ShaunG-RU/DRC-Project/LTspice/RMS Based Compressor - Alternative Design/DRC.asc

Attack: res; 0
B2: bv; V=(white(2e6*time)/100)
C1: cap; 0.01µ
C2: cap; 0.01µ
C3: cap; 0.01µ
C4: cap; 22p
C5: cap; 10µ
C7: cap; 0.1µ
C10: cap; 1µ
C11: cap; 100p
D1: diode; 1N4148
D2: diode; 1N4148
D3: diode; 1N4148
D4: diode; 1N4148
R1: res; 20k
R2: res; 10k
R3: res; 20k; tol=1
R4: res; 10k
R5: res; 10k
R6: res; 52.3
R7: res; 4.7
R8: res; 2k
R9: res; 2k
R10: res; 162k
R11: res; 500
R12: res; 500
R13: res; 5.1k
R14: res; 2k
R15: res; 680k
R16: res; 10k
R17: res; 40k
R18: res; 2k
R19: res; 2k
R22: res; 243k
R23: res; 25k
R24: res; 25k
R29: res; 10Meg
R30: res; 10Meg
R31: res; 84.5k
R32: res; 750k
R33: res; 10Meg
THAT1: THAT2181A
U1: OP1177
U2: OP1177
U3: AD8310
U4: OP1177
U5: OP1177
U9: LTC1966
U12: LT1494
V1: voltage; 12
V2: voltage; -12
V3: voltage; 5
V4: voltage; -5
V5: voltage; wavefile=lickpick.wav
V6: voltage; 1.9
V7: voltage; wavefile=lickpick.wav
V8: voltage; 4
Named nets: INPUT, V+, V-, ABS, 0, Vdd, Vss, RMS, LOG, INPUT2, THRESHOLD, GAIN, VCA
.SUBCKT THAT2181A  1   2   3   4   5   6   7   8 
*(lin, Ec+, Ec-, Sym, Vee, GND, Vcc, Iout)
R1         10 13  2.5k  
R2         10 14  2.5k  
I1         10 29 DC 50uA  
R3         11 7  8k  
R4         12 7  8k  
G1         7 15 11 12 1.25e-4
R5         0 15  10MEG  
R6         0 16  10k  
C1         16 15  10p  
R7         19 7  2k  
G2         19 20 15 0 5e-4
C2         19 7  8p  
E1         20 28 30 0 2
R8         5 29  1.7k  
V1         0 29 DC 2.1V  
I2         0 30 DC 20uA  
R9         4 2  27  
C3         20 0  12p  
I3         20 28 DC 220uA  
V2         18 0 DC .7V  
V3         17 15 DC 1.4V  
Q1         11 1 13 QNHIB 
Q2         12 9 14 QNHIB 
Q3         20 21 23 QNPNNOM 
Q4         20 22 24 QNPNNOM 
Q5         8 4 27 QNPNNOM 
Q6         1 25 26 QNPNNOM 
Q7         1 2 23 QPNPNOM 
Q8         8 3 24 QPNPNOM 
Q9         28 28 27 QPNPNOM 
Q10        28 28 26 QPNPNOM 
Q11        28 29 5 QNPNNOM 
Q12        30 30 31 QNPNNOM 
Q13        0 0 31 QPNPNOM 
D1         18 15 DNOM 
D2         17 7 DNOM 
R10        3 25  22  
R11        22 20 22  
R12        21 20 27  
Vos        9 6 DC 3mV  
.model qnpnnom npn (is=1e-15 bf=200, vaf=110, cjc=3pF)
.model qpnpnom pnp (is=1e-15 bf=100, vaf=85, cjc=5pf)
.model qnhib npn (bf=16000)
.model dnom d (is=1e-15)
.ENDS
.tran 250m
