ShaunG-RU/DRC-Project/LTspice/Peak Detector/Peak Detector.asc

C1: cap; 10n
C2: cap; 4.7n
C3: cap; 10n
C4: cap; 4.7n
C5: cap; 100n
D1: diode; 1N4148
D2: diode; 1N4148
D3: diode; 1N4148
D4: schottky; CMDSH2-3
D5: schottky; CMDSH2-3
D6: schottky; BAT54
D7: diode; 1N4148
D8: diode; 1N4148
D9: schottky; BAT54
Q1: npn
Q2: npn
R1: res; 47k
R2: res; 47k
R3: res; 100
R4: res; 10k
R5: res; 33
R6: res; 10Meg
R7: res; 10k
R8: res; 10k
R9: res; 10k
R10: res; 1k
R11: res; 10k
R12: res; 10k
R13: res; 33
R14: res; 10Meg
R15: res; 10k
R16: res; 100k
R17: res; 10k
R18: res; 10k
R19: res; 1k
R20: res; 10k
R21: res; 10k
R22: res; 200
R23: res; 200
R24: res; 500k
U1: AD549
U2: AD549
U3: AD549
U4: AD549
U5: AD549
U6: AD549
U7: AD549
U8: AD549
V1: voltage; PULSE(0 1 0 1p 1p 100u 200u 5)
V2: voltage; -15
V3: voltage; 15
V4: voltage; SINE(0 1 10000 2.5m 0 0 5)
V5: voltage; SINE(0 3 10000 5m)
Named nets: 0, ABS, PEAK2, Vss, PEAK, PEAK3, V+, V-, PEAK0, Vdd
.tran 5m
