ShaunG-RU/DRC-Project/LTspice/Envelope Detector with Attack and Release Control/envelope det.asc

C1: cap; 1µ
C2: cap; 10µ
C3: cap; 10µ
D1: diode
D2: diode
D3: diode
D4: diode
R1: res; 20k
R2: res; 20k
R3: res; 100k
R4: res; 1k
R5: res; 10k
U1: AD549
U2: AD549
U3: AD549
U4: AD549
V1: voltage; SINE(0 1 1k)
V2: voltage; 15
V3: voltage; -15
Named nets: V+, V-, 0
.tran 10m
