ShaunG-RU/DRC-Project/LTspice/RMS and Peak Based Compressor with Knee Control/Knee Control DRC.asc

B1: bv; V=1.414*0.775*(10**({dBu_level}/20))*V(1V)
B2: bv; V=V(1V)*sin({modfreq}*2*pi*time)
B3: bv; V=20*log10(abs(V(signal_in))) -20*log10(abs(V(final)))
B4: bv; V=V(final)/(1.414*0.775*(10**({dBu_level}/20)))
C1: cap; 0.1µ; V=50 Irms=0 Rser=0.09 Lser=0
C2: cap; 0.1µ
C3: cap; 0.2n; V=25 Rser=0.2
C4: cap; 0.3n; V=50 Irms=0 Rser=0.1 Lser=0
C5: cap; 0.1µ; V=10 Irms=0 Rser=0.003 Lser=0
C6: cap; 10µ; Rser=0.09
C8: cap; 22p; V=50 Irms=0 Rser=0.1601 Lser=520p mfg="Würth Elektronik" pn="885012008039 WCAP-CSGP 1206" type="NP0"
C9: cap; 1µ
C10: cap; 0.1µ; V=10 Irms=0 Rser=0.003 Lser=0
C11: cap; 0.3n; V=50 Irms=0 Rser=0.1 Lser=0
C12: cap; 1µ
C13: cap; 0.1µ; V=10 Irms=0 Rser=0.003 Lser=0
C14: cap; 0.2n; V=25 Rser=0.2
C15: cap; 1µ
C16: cap; 10µ
C17: cap; 1µ
C18: cap; 0.1µ; V=50 Irms=0 Rser=0.09 Lser=0
C19: cap; 0.1µ
D1: diode; 1N4148
D2: diode; 1N4148
D3: diode; 1N4148
D4: diode; 1N4148
D5: diode; 1N4148
D8: diode; 1N4148
D10: schottky; RB500SM-30
D12: diode; 1N4148
D14: diode; 1N4148
D19: diode; 1N4148
I1: current; 255.8µ
Q1: npn; 2N3904
Q2: npn; 2N3904
R1: res; 47.6K
R2: res; 10K
R3: res; 6.8K
R4: res; 6.8K
R5: res; 6.8K
R6: res; 3.4K
R7: res; 6.8K
R8: res; 4.2k
R9: res; 4.2k
R10: res; 5k
R11: res; 2K
R12: res; 2K
R13: res; 100K
R14: res; 100K
R15: res; 100K
R16: res; 100K
R17: res; 10K
R18: res; 10K
R19: res; 10K
R20: res; 10K
R21: res; 1k
R22: res; 10k
R23: res; 10k
R24: res; 10K
R25: res; 10K
R26: res; 35k
R27: res; {release}
R28: res; {attack}
R29: res; {attack}
R30: res; 10k
R31: res; 10k
R32: res; 10K
R33: res; 10K
R34: res; 250
R36: res; 10k
R37: res; 10K
R40: res; 10k
R41: res; 1k
R42: res; 1k
R43: res; 20
R44: res; 10K
R45: res; 10K
R46: res; 1k
R47: res; 4k
R48: res; 1k
R49: res; 1k
R50: res; 10k
R51: res; 10k
R52: res; 100k
R53: res; 100k
R54: res; 100k
R55: res; 100k
R56: res; 10k
R57: res; 10k
R58: res; 20K
R59: res; 20K
R60: res; 10Meg
R61: res; 5.1K
R62: res; 14k
R63: res; 100k
R65: res; {tanh_gain_in}
R66: res; 10k
R67: res; 250
R68: res; 10k
R69: res; 10k
R71: res; 1k
R72: res; 2k
R73: res; 10k
R74: res; 30.808k
R75: res; 1k
R76: res; 30.808k
R77: res; 1k
R78: res; 1k
R80: res; 200k
R81: res; 100k
R82: res; 20
R83: res; 1k
R84: res; 4k
R85: res; 100k
R86: res; 100k
R87: res; 10k
R88: res; 10k
R89: res; 10k
U1: TL072
U2: LTC6244
U3: LTC6244
U4: TL072
U5: TL072
U6: TL072
U7: TL072
U8: pot; T={threshold}
U9: TL072
U10: TL072
U11: pot; R=1k; T= 1/{ratio_ctrl} stiff=10000
U12: TL072
U13: TL072
U14: LT1217
U15: TL072
U16: TL072
U17: pot; T={knee}
U18: TL072
U19: TL072
U20: TL072
U21: TL072
U22: TL072
U23: VCA824
U24: TL072
U25: TL072
U26: pot; T=.4917
U27: TL072
U28: THAT2180A
U29: TL072
U30: TL072
U31: TL072
U32: LTC6244
U33: LT1217
U35: TL072
U36: LTC6244
U37: LT1217
U38: TL072
U39: pot; R=1meg; T=.8029
U40: LTC6244
U41: VCA824
U42: pot; T=.4917
U43: pot; R=1meg; T=.8033
U44: TL072
U45: LTC6244
U46: TL072
U47: TL072
V2: voltage; +15V
V3: voltage; -15V
V4: voltage; SINE(0 1 {freq})
V5: voltage; PULSE(-1 1 0 {1/(2*freq)} {1/(2*freq)} 0 {1/freq})
V6: voltage; 5V
V7: voltage; ""; AC 1.736
V8: voltage; 5V
V9: voltage; 0V
V10: voltage; PULSE(-1 1 0 1e-6 1e-6 {duty/freq} {1/freq})
V11: voltage; PULSE(0 1 20ms 1e-6 1e-6 0.1 0 1)
V12: voltage; -5V
V17: voltage; 0
V19: voltage; SINE(0 0.1 50)
V20: voltage; -0.5V
X1: 
X3: 
X4: 
X5: 
X6: 
X7: 
X8: 
X9: 
X10: 
X11: 
X12: 
X13: 
X14: 
X15: 
X16: 
X17: 
X18: 
X19: 
X20: 
X21: 
X22: 
X23: 
Named nets: 0, +15V, -15V, 1V, full_rect, full_rect_log, 1Vramp, tanh_out, full_rect_log_min_thr, thr_log, peak_AR, gain_before_ratio, gain_before_ratio_inv, 1Vmod, gain_after_ratio, +5V, -5V, signal_in, final, gain_final, tanh_out_gain_inv, tanh_out_clamp, vratio_buf, tanh_out_clamp2, tanh_out_clamp2_clip_buf, peak_AR_buf_tanh, gain_reduction, final_norm, lin_thr, vratio, vratio_buf_inv, 1Vsquare, signal_in_ac, tanh_norm, vratio_buf_sym, -0.5V, tanh_out_shift, full_rect_log_min_thr_clip2, 1Vpulse, full_rect_log_min_thr_clip, vhalf_kw, vhalf_kw_inv, full_rect_log_min_thr_min_half_kw, 4dBu, vhalf_kw_buf
Conversion from 1V max to dBu_level.
Circuit nominal is 4dBu
1V reference sine for tests
PRECISION FULL WAVE RECTIFIER
linear to log signal converter
gain 5.76 so that we get 10V at 4dBU for rectifier stage
op amp buffer to make output impedance as low as possible 
as the following rectifier stage is sensitive to it
log stage transfer function Vout=   -Vt*ln(Vin/(Is*R))
Vt = diode thermal voltage, Is = diode saturation current
thermal voltage depends on absolute temperature, which would go up with room temperature
and high signal levels (more current flowing in the diodes = more heat)
thermal management may be advised, ex: both diodes for signal and threshold could be termally
coupled.
Also advised to match both diodes
linear to log threshold converter
THRESHOLD POT
out = full_rect_log - thr_log
thr_log more negative = higher threshold
wiper closer to 1 = lower threshold
wiper closer to 0 = higher threshold
LOG DOMAIN PEAK DETECTOR +  EXP A/R
release potentiometer
attack potentiometer
input offset compensation
output offset compensation
RAILS
.param modfreq = {10}
.param freq = {20}
What we have is a smooth transition between unity gain setpoint (0V), ratio = 1
and set ratio voltage.
1V amplitude modulated sine for tests
1V triangle
gain reduction quick&dirty (zoom to get rid of singularities)
.tran 0 0.2 1ms {1/sample_rate} uic
.param dBu_level = {4}
.param sample_rate = 44.1k
.options cshunt=1e-15
TEST BENCH
compressor output
KNEE MANAGEMENT
SIGNAL(dB) - THRESHOLD(dB) STAGE
tanh() cell using a BJT differential pair
tanh() saturation... low R65 looks more like sine. (very soft knee)
 very high R65 introduces high distortion at knee. (folding)
RATIO POT
clamp tanh_out_gain_inv output positive excursions to -vratio level (positive value).
should not happen unless tanh() current sink is above 247µA.
then,  tanh_out_gain_inv may go above -vratio.
gain = gain_before_ratio*( 1 - 1/ratio)
gain = gain_before_ratio + gain_before_ratio_inv/ratio  (gain_after_ratio_inv is negative)
gain = gain_before_ratio + gain_after_ratio (gain_after_ratio is negative)
AUDIO PATH VCA STAGE - FEEDFORWARD
;ac dec 10 20 100000
1V square
.param duty = {0.5}
Here 0V level is threshold +kw/2. The point at which the compressor should start working
we clip signal under 0V
lin_v = 15*(1-t)*10k/(10k +5k)
the incentive to use a lin to log diode converter instead of a log pot is :
use the same transfer function. (make calibration easier)
have the thermal effect partially cancel each other (since both diode networks heat more or less
the same way, but that is assuming current is the same which is not because the threshold
diode  is subject to DC)
The peak detector A/R stage contribution is made negligible by setting the fastest A/R possible,
R=100 ohms for both
we ommit input gain = 5.76 because both vin and vthr use the same gain so it cancels out.
technically we could ommit Is*R because they also cancel out...
 
n*-Vt*ln(Vin/(Is*R))
25.4mV*ln(Vin/(2nA*4.2k))
deltaVln = 25.4mV*ln(Vin/(2nA*4.2k)) - 25.4mV*ln(Vthr/(2nA*4.2k)) 
deltaVln = 25.4mV*(ln(Vin/(2nA*4.2k)) - ln(Vthr/(2nA*4.2k)))
deltaVln = 25.4mV*(ln(Vin) - ln(Vthr)  -ln(2nA*4.2k) + ln(2nA*4.2k))
 
now convert ln2 to log10, hence the factor 2.303 and then to dBV...
 
deltaVllog = (25.4mV*2.303)*(log(Vin) - log(Vthr))
deltaVllog = (25.4mV*2.303)*(log(Vin) - log(Vthr))
dbV = 20*log(V)
we want k*25.4mV*2.303 = 20
k =20/(2.303-*25.4mV)
k = 341.9
and we also have THAT2180 1 dbV gain = 0.0061V
thus final normalization gain = 341.9*0.0061 = 2.08559
k = 2.08559
use good audio cap here
gain_final OUTPUT impedance should be as low as possible to drive THAT2180 properly
Z_out << 50 Ohms.
compare that to TL072 125ohms open loop resistance.
That's why we use a high current low output impedance LT1217 Op Amp
gain_in 1 + R74/R75 (here 30.808/1 +1 = 31.808) so that we renormalize to 10V max
max log_min_thr (4dbU triangle signal, threshold -INF dB) =  0.31425V
we're back to 0.314V max
R67 current limiting resistor to protect U14
R79 current limiting resistor to protect U33
THEORY = 25.4mV*ln(Vin*5.76/(2nA*4.2k))
 25.4mV*ln(10/(2nA*4.2k)) = 0.355325
gain_before ratio has to stay under 1.6V !!! as per VCA824 datasheet
;.noise V(final) V7 dec 10 1 20000
0.1% or less
0.1% or less
0.1% or less
0.1% or less
D8 and D4 must be matched and coupled thermally
input offset compensation
output offset compensation
input signal amplitude could be as high as 10V
symmetry point is 0.5V this is an inverting op amp with 0.5V reference symmetry.
used to properly condition the gain signal of the VCA824 (U41) that performs tanh() normalization
inverting op amp
tanh() normalizer ( so that : vratio_buf < tanh_norm < 0V )
this assumes that the previous tanh() cell is well behaved and  -0.5V < tanh_out < 0.5V
if not, the following clamping stage will take care of unwanted excursions.
a bit of extra precaution so that VG fed to the U23 VCA824 never goes above 0V.
tanh() normalization and clamping action is not perfect, as well as U41 VCA824 always 
has some offset despite calibration, so we clip above 0V here.
clamping is also required if tanh() current source is also set above 247µA
tweak 200 < R65 < 1.5k
.param bw = {0.05}
here we clip signal under -kw/2 and above kw/2 0V is threshold
bw is the threshold bandwidth for soft/hard knee application
setting I1 above 247µA gives a tanh() output that is no more bound from [-0.5V to 0.5V]
Normalization and shifting to 0.5 is no more sufficient to set final ratio signal inside [vratio, 0V] range. 
however, clamping at -vratio and clipping at 0V before the U23 VCA824 make the
circuit compensated once again should that happen.
1V square pulse
for testing A/R constants
account for diode drop in final gain.
attack range 100 - 10k
release range 10k - 10Meg
RATIO = 1/T
vratio =  T - 1
GAIN COMPUTER (U23 with variable ratio for knee management and U25 for final gain)
FINAL GAIN NORMALIZATION
CURRENT TO VOLTAGE
CURRENT LIMITING
KNEE WIDTH POT
KW = 1 - T
We offset down the selected threshold by half knee width.
This to ensure smooth knee application, so that the gain computer and knee width start
working at the same levels
decoupling A/R with diodes is one way to do it, but it introduces a diode voltage drop.
It is mainly experimental. The more standard way is to use separate attack/release stages
separated by a buffer
the sidechain and the audio path branches before the capacitor and each uses different caps
it may create phase problems. You can try using a single cap.
quite experimental. may introduce distortion for small knee widths (hard knee = distortion)
this is because of the use of the tanh() function
.param knee=0.95
.param ratio_ctrl=100
.param threshold = 0.5
LP filter potentiometer
.param attack = 100
.param release = 100
COMPRESSOR PARAMETERS
;.step param knee 0.85 0.98 0.02
;.step param ratio_ctrl 1 50 5
;.step param attack 0.3 1 0.1
.step dec param tanh_gain_in 100 10000 3
.param tanh_gain_in = 4000
35.3456k
ratio_ctrl not the actual ratio
APPROXIMATIVE TABLE :
ratio_ctrl      ratio
6                 1.31
11                1.85
16                2.47
21                3.22
26                4.11
31                5.22
36                6.25
41                8.4
46                10.2
51                 12.2
;.step param threshold 0.1 1 0.1
www.skynext.tech
Author : R.Verissimo
release 0.91 05/09/2023
.SUBCKT pot 1 2 3 T=0.5 R=10k
.param tap={limit(T,1m,.999)}
R0 1 3 {R*(1-tap)}
R1 3 2 {R*tap}
.ENDS
 
.SUBCKT exppot 1 2 3 T=0.5
.param tap={limit(T,1m,.999)}
.param stiff={limit(stiff,1,10000)}
 
R0 1 3 {R*exp(-tap*ln(R*stiff))}
R1 3 2 {R*(1-exp(-tap*ln(R*stiff)))}
.ENDS
*                 Iin          
*                  |  Ec+ 
*                  |   |   Ec-
*                  |   |   |  Vee 
*                  |   |   |   |  GND
*                  |   |   |   |   |  Vcc 
*                  |   |   |   |   |   |  Iout
*                  |   |   |   |   |   |   |
.SUBCKT THAT2180A  1   2   3   4   5   6   7 
*
*
*
R1         10 13  2.5k  
R2         10 14  2.5k  
I1         10 29 DC 50uA  
R3         11 7  8k  
R4         12 7  8k  
G1         7 15 11 12 1.25e-4
R5         0 15  10MEG  
R6         0 16  10k  
C1         16 15  10p  
R7         19 7  2k  
G2         19 20 15 0 5e-4
C2         19 7  8p  
E1         20 28 30 6 2
R8         5 29  1.7k  
V1         0 29 DC 2.1V  
I2         0 30 DC 20uA  
R9         4 2  27  
C3         20 0  12p  
I3         20 28 DC 220uA  
V2         18 0 DC .7V  
V3         17 15 DC 1.4V  
Q1         11 1 13 QNHIB 
Q2         12 9 14 QNHIB 
Q3         20 21 23 QNPNNOM 
Q4         20 22 24 QNPNNOM 
Q5         8 4 27 QNPNNOM 
Q6         1 25 26 QNPNNOM 
Q7         1 2 23 QPNPNOM 
Q8         8 3 24 QPNPNOM 
Q9         28 28 27 QPNPNOM 
Q10        28 28 26 QPNPNOM 
Q11        28 29 5 QNPNNOM 
Q12        30 30 31 QNPNNOM 
Q13        0 0 31 QPNPNOM 
D1         18 15 DNOM 
D2         17 7 DNOM 
R10        3 25  20  
R11        22 20 20 
R12        21 20 27  
Vos        9 6 DC 3mV  
Isym       0 4 DC -420nA  
*    Isym = -420nA for typical THD.  Set to -1uA for worst case THD.
.model qnpnnom npn (is=1e-15 bf=200, vaf=110, cjc=3pF)
.model qpnpnom pnp (is=1e-15 bf=100, vaf=85, cjc=5pf)
.model qnhib npn (bf=16000)
.model dnom d (is=1e-15)
.ENDS
*                      Positive Supply
*                      |   Gain Control
*                      |   |   Non-Inverting Input 
*                      |   |   |   Gain Setting Resistor Terminals
*                      |   |   |     |   |  Inverting Input
*                      |   |   |     |   |    |  Negative Supply
*                      |   |   |     |   |    |   |  Reference Voltage 
*                      |   |   |     |   |    |   |   |  Output
*                      |   |   |     |   |    |   |   |    |
*                      |   |   |     |   |    |   |   |    |    Feedback
*                      |   |   |     |   |    |   |   |    |      |
.SUBCKT VCA824 +Vcc VG +Vin +Rg -Rg -Vin -Vcc Vref Out Gnd FB
 
X_U5_F8    U5_N00257 U5_N00297 N09821 -VCC VCA82X_BIAS_U5_F8 
X_U5_F1    U5_N00167 U5_N00177 +VCC N06304 VCA82X_BIAS_U5_F1 
V_U5_V1         U5_N00167 U5_N00195 0.433V
E_U5_E1         U5_N00195 -VCC +VCC -VCC 0.5
X_U5_F6    U5_N00297 U5_N00251 N08923 -VCC VCA82X_BIAS_U5_F6 
X_U5_F3    U5_N00177 U5_N00183 +VCC N08572 VCA82X_BIAS_U5_F3 
X_U5_F4    U5_N00183 U5_N00189 +VCC N08740 VCA82X_BIAS_U5_F4 
X_U5_F2    U5_N00189 U5_N00257 +VCC N10100 VCA82X_BIAS_U5_F2 
X_U5_F5    U5_N00251 U5_N00205 N07015 -VCC VCA82X_BIAS_U5_F5 
R_U5_R3         U5_N00195 U5_N00205  1k  
Q_U6_Q24         N06304 U6_N16946 U6_N15431 NPN8 {x1}
R_U6_R15         U6_N26012 +VCC  300  
R_U6_R20         U6_N49467 U6_N46592  100  
R_U6_R24         -VIN U6_N336522  150  
Q_U6_Q23         U6_N00503 U6_N16946 U6_N13215 NPN8 {x6}
C_U6_C3         U6_N334753 U6_N334801  10m  TC=0,0 
C_U6_C1         U6_N00709 U6_N22036  0.5p  
Q_U6_Q28         U6_N22036 U6_N07222 U6_N26012 PNP8 {x6}
Q_U6_Q29         U6_N07222 U6_N07222 U6_N612661 PNP8 {x2}
Q_U6_Q37         U6_N49467 U6_N16946 U6_N49758 NPN8 {x6}
R_U6_R13         -VCC U6_N19410  2k  
D_U6_U1         U6_N334753 U6_N334759 dn3 
R_U6_R21         U6_N57293 +VCC  300  
Q_U6_Q30         N07015 U6_N07222 U6_N29549 PNP8 {x2}
R_U6_R18         -VCC U6_N36767  160  
R_U6_R25         U6_N3853581 +RG  10  
Q_U6_Q32         +RG U6_N16946 U6_N36767 NPN8 {x6}
E_U6_E1         U6_N00709 -VCC +VCC -VCC 0.5
R_U6_R23         +VIN U6_N336330  150  
Q_U6_Q36         U6_N46276 U6_N46276 U6_N46592 NPN8 {x14}
I_U6_I1         U6_N334759 U6_N334753 DC 1.5u  
Q_U6_Q26         U6_N16946 U6_N16946 U6_N19410 NPN8 {x2}
Q_U6_Q25         +VCC N06304 U6_N16946 NPN8 {x2}
Q_U6_Q40         U6_N42606 U6_N07222 U6_N57293 PNP8 {x6}
Q_U6_Q22         U6_N04782 U6_N04782 U6_N10900 NPN8 {x14}
Q_U6_Q21         +VCC U6_N336330 U6_N04782 NPN8 {x14}
R_U6_R14         U6_N612661 +VCC  2k  
R_U6_R17         -VCC U6_N13215  160  
Q_U6_Q34         +VCC U6_N336522 U6_N46276 NPN8 {x14}
Q_U6_Q33         N08372 U6_N22036 +RG NPN8 {x14}
R_U6_R22         -VCC U6_N51427  160  
E_U6_E2         U6_N334759 -VCC +VCC -VCC 0.5
R_U6_R19         -VCC U6_N49758  160  
Q_U6_Q27         U6_N22036 +RG U6_N00503 NPN8 {x14}
Q_U6_Q31         -VCC N07015 U6_N07222 PNP8 {x2}
C_U6_C2         U6_N00709 U6_N42606  0.5p  
Q_U6_Q38         U6_N42606 -RG U6_N49467 NPN8 {x14}
X_U6_F1    U6_N334801 U6_N334759 U6_N336330 U6_N334759
+  VCA82X_INPUT_BUFFER_U6_F1 
R_U6_R11         U6_N29549 +VCC  900  
E_U6_E4         U6_N3853202 -VCC +VCC -VCC 0.5
Q_U6_Q39         -RG U6_N16946 U6_N51427 NPN8 {x6}
R_U6_R16         U6_N00503 U6_N10900  100  
R_U6_R12         -VCC U6_N15431  955  
Q_U6_Q35         N08468 U6_N42606 -RG NPN8 {x14}
C_U6_C5         U6_N3853202 U6_N3853581  0.88p  TC=0,0 
R_U7_R27         -VCC U7_N01059  800  
Q_U7_Q56         U7_N65219 U7_N65219 U7_N64914 NPN8 {x4}
Q_U7_Q60         U7_N107420 U7_N89137 U7_N81704 NPN8 {x12}
Q_U7_Q86         U7_N168308 U7_N167450 U7_N168596 NPN8 {x16}
Q_U7_Q77         U7_N137141 U7_N137141 U7_N142127 PNP8 {x16}
R_U7_R25         GND U7_N89137  50  
R_U7_R23         -VCC U7_N01019  100  
Q_U7_Q59         U7_N86791 U7_N65219 U7_N01059 NPN8 {x1}
R_U7_R28         -VCC U7_N01061  200  
R_U7_R32         GND U7_N160714  50  
R_U7_R17         -VCC U7_N55967  100  
R_U7_R37         U7_N145504 +VCC  110  
Q_U7_Q45         U7_N34597 U7_N34597 U7_N34298 PNP8 {x12}
Q_U7_Q87         U7_N167450 U7_N167450 U7_N168824 NPN8 {x16}
Q_U7_Q84         U7_N165781 U7_N165781 U7_N168308 NPN8 {x16}
Q_U7_Q62         U7_N01231 U7_N65219 U7_N01061 NPN8 {x4}
R_U7_R11         U7_N34298 +VCC  160  
Q_U7_Q79         U7_N01317 U7_N142759 U7_N145504 PNP8 {x16}
Q_U7_Q80         N08740 U7_N01231 U7_N137141 PNP8 {x16}
Q_U7_Q52         U7_N53649 U7_N65219 U7_N55659 NPN8 {x8}
R_U7_R22         U7_N81704 U7_N82314  1k  
Q_U7_Q49         U7_N01387 U7_N01387 U7_N37408 PNP8 {x12}
R_U7_R21         U7_N01001 +VCC  740  
Q_U7_Q78         U7_N142759 U7_N142759 U7_N145276 PNP8 {x16}
R_U7_R13         U7_N1695201 VG  50  
Q_U7_Q61         U7_N116536 U7_N86791 U7_N82314 NPN8 {x12}
Q_U7_Q88         N08740 U7_N160714 N08923 NPN8 {x2}
Q_U7_Q65         U7_N01387 U7_N01387 U7_N107420 NPN8 {x12}
Q_U7_Q63         U7_N01317 U7_N65219 U7_N01207 NPN8 {x4}
R_U7_R34         U7_N142127 +VCC  110  
Q_U7_Q85         FB U7_N165781 U7_N167450 NPN8 {x16}
R_U7_R39         N08923 U7_N1690600  50  
Q_U7_Q70         U7_N119904 U7_N119904 U7_N122147 PNP8 {x16}
R_U7_R29         -VCC U7_N01207  200  
Q_U7_Q55         N08572 U7_N65219 U7_N67656 NPN8 {x2}
Q_U7_Q71         U7_N122683 U7_N122683 U7_N119904 PNP8 {x16}
R_U7_R31         -VCC U7_N168596  200  
Q_U7_Q68         U7_N116528 U7_N116512 U7_N01001 PNP8 {x12}
Q_U7_Q69         U7_N116536 U7_N116536 U7_N116528 PNP8 {x12}
Q_U7_Q74         U7_N122683 U7_N01351 N08468 NPN8 {x16}
R_U7_R26         U7_N86791 GND  4.1k  
R_U7_R24         -VCC U7_N01017  100  
Q_U7_Q57         U7_N81704 U7_N65219 U7_N01017 NPN8 {x8}
R_U7_R38         U7_N122147 +VCC  110  
Q_U7_Q47         U7_N37110 U7_N34597 U7_N34058 PNP8 {x12}
Q_U7_Q51         U7_N01387 U7_N45862 U7_N53649 NPN8 {x12}
Q_U7_Q46         U7_N01351 U7_N37408 U7_N34597 PNP8 {x12}
Q_U7_Q50         U7_N01351 U7_N1695201 U7_N51592 NPN8 {x12}
R_U7_R18         -VCC U7_N55659  100  
Q_U7_Q81         FB U7_N01317 U7_N142759 PNP8 {x16}
R_U7_R16         -VCC U7_N67656  400  
R_U7_R15         U7_N51592 U7_N53649  1k  
Q_U7_Q66         U7_N116512 U7_N116512 U7_N01003 PNP8 {x12}
R_U7_R35         U7_N145276 +VCC  110  
Q_U7_Q72         U7_N122683 U7_N01351 N08372 NPN8 {x16}
R_U7_R19         -VCC U7_N64914  1.4k  
Q_U7_Q58         U7_N82314 U7_N65219 U7_N01019 NPN8 {x8}
R_U7_R30         -VCC U7_N168824  200  
R_U7_R20         U7_N01003 +VCC  740  
R_U7_R12         U7_N34058 +VCC  160  
Q_U7_Q53         U7_N51592 U7_N65219 U7_N55967 NPN8 {x8}
Q_U7_Q76         U7_N01231 U7_N137141 U7_N141896 PNP8 {x16}
Q_U7_Q54         +VCC N08572 U7_N65219 NPN8 {x4}
Q_U7_Q67         U7_N107420 U7_N116536 U7_N116512 PNP8 {x12}
R_U7_R36         U7_N141896 +VCC  110  
R_U7_R33         U7_N142127 U7_N145276  2k  
Q_U7_Q73         U7_N01231 U7_N01387 N08372 NPN8 {x16}
Q_U7_Q75         U7_N01317 U7_N01387 N08468 NPN8 {x16}
Q_U7_Q48         U7_N37408 U7_N37408 U7_N37110 PNP8 {x12}
Q_U7_Q64         U7_N01351 U7_N01351 U7_N107420 NPN8 {x12}
R_U7_R14         GND U7_N45862  50  
Q_U7_Q82         U7_N165781 U7_N1690600 N08740 PNP8 {x16}
Q_U8_Q38         U8_N01099 U8_N38844 U8_N39084 PNP8 {x14}
R_U8_R18         U8_N01099 U8_N82756  125  
Q_U8_Q49         U8_N78893 U8_N78893 U8_N80276 NPN8 {x5}
E_U8_E2         U8_N389559 -VCC +VCC -VCC 0.5
R_U8_R24         U8_N163888 FB  0.01  
R_U8_R23         VREF U8_N52536  10  
R_U8_R10         U8_N23775 U8_N13605  600  
Q_U8_Q47         U8_N75689 U8_N78893 U8_N73458 NPN8 {x3}
R_U8_R13         U8_N00843 U8_N13605  250  
X_U8_F1    U8_N389453 U8_N389559 VREF U8_N389559 VCA821_4_OUTPUT_STAGE_U8_F1 
Q_U8_Q45         U8_N63102 N10100 U8_N66552 NPN8 {x2}
C_U8_C7         U8_N00839 U8_N13605  0.85p  TC=0,0 
Q_U8_Q39         U8_N13605 U8_N38844 U8_N84507 NPN8 {x14}
Q_U8_Q52         OUT U8_N91269 -VCC NPN8 {x60}
Q_U8_Q36         U8_N39084 U8_N31052 U8_N32378 PNP8 {x6}
R_U8_R16         U8_N01099 U8_N80276  150  
Q_U8_Q43         U8_N75689 U8_N63102 U8_N163888 PNP8 {x8}
R_U8_R21         +VCC U8_N13605  20  
Q_U8_Q50         U8_N84507 U8_N78893 U8_N82756 NPN8 {x6}
C_U8_C8         U8_N01099 U8_N80276  0.85p  TC=0,0 
Q_U8_Q33         U8_N01025 N09821 U8_N24027 PNP8 {x2}
Q_U8_Q41         U8_N35588 U8_N01025 U8_N163888 NPN8 {x8}
R_U8_R11         U8_N01099 U8_N67452  600  
D_U8_D14         U8_N73458 U8_N01099 DX 
Q_U8_Q42         U8_N63102 U8_N63102 U8_N52536 PNP8 {x8}
Q_U8_Q35         U8_N31052 U8_N31052 U8_N00839 PNP8 {x5}
Q_U8_Q32         U8_N24027 U8_N24027 U8_N23775 PNP8 {x2}
Q_U8_Q51         U8_N91269 U8_N91269 -VCC NPN8 {x60}
D_U8_D17         U8_N163888 U8_N1399050 DX 
Q_U8_Q62         U8_N01099 U8_N38844 U8_N39084 PNP8 {x8}
Q_U8_Q61         U8_N13605 U8_N38844 U8_N84507 NPN8 {x8}
D_U8_U1         U8_N389449 U8_N389559 dn3
Q_U8_Q34         U8_N35588 U8_N31052 U8_N00843 PNP8 {x3}
C_U8_C2         U8_N38844 U8_N13605  0.89p  
D_U8_D18         U8_N1399050 U8_N52536 DX 
R_U8_R12         U8_N01099 U8_N67680  600  
Q_U8_Q59         U8_N114858 U8_N114858 +VCC PNP8 {x60}
D_U8_D16         U8_N1375710 U8_N163888 DX 
Q_U8_Q46         U8_N66552 U8_N66552 U8_N67680 NPN8 {x2}
Q_U8_Q44         N10100 U8_N66552 U8_N67452 NPN8 {x2}
Q_U8_Q60         OUT U8_N114858 +VCC PNP8 {x60}
R_U8_R14         U8_N00839 U8_N13605  150  
Q_U8_Q58         U8_N114858 U8_N39084 OUT NPN8 {x60}
I_U8_I1         U8_N389559 U8_N389449 DC 3.12u  
Q_U8_Q37         U8_N38844 U8_N35588 U8_N31052 PNP8 {x3}
R_U8_R17         U8_N32378 U8_N13605  125  
C_U8_C3         U8_N01099 U8_N38844  0.89p  
R_U8_R9         U8_N19796 U8_N13605  600  
Q_U8_Q48         U8_N38844 U8_N75689 U8_N78893 NPN8 {x3}
R_U8_R19         -VCC U8_N01099  20  
D_U8_D12         U8_N13605 U8_N00839 DX 
Q_U8_Q31         N09821 U8_N24027 U8_N19796 PNP8 {x2}
D_U8_D13         U8_N52536 U8_N1375710 DX 
R_U8_R25         OUT OUT  10  
Q_U8_Q53         U8_N91269 U8_N84507 OUT PNP8 {x60}
C_U8_C6         U8_N389449 U8_N389453  10m  
D_U8_D11         U8_N13605 U8_N00843 DX 
Q_U8_Q40         U8_N01025 U8_N01025 U8_N52536 NPN8 {x8}
R_U8_R15         U8_N01099 U8_N73458  250  
D_U8_D15         U8_N80276 U8_N01099 DX 
 
.PARAM  x4={x2*2} x5={x1*5} x12={x6*2} x6={x2*3} x24={x1*24} x8=1 x14={x2*7}
+  x16={x8*2} x18={x1*18} x90={x1*90} x60={x12*5} x1={x2/2} x2={x8/4} x30={x1*30}
+  x3={x1*3}
 
.MODEL DN3 D( IS=.1F AF=1.0 KF=39.0E-17)
 
.model dx       d(is=0.1p rs=.1 cjo=2p tt=1p bv=100 ibv=0.1p)
 
.model NPN8 npn
 
+ is=7.604e-018
+ bf=157
+ nf=1
+ vaf=78.71
+ ikf=0.03975
+ ise=3.219e-014
+ ne=2
+ br=0.7614
+ nr=1
+ var=1.452
+ ikr=0.08172
+ isc=7.618e-021
+ nc=1.847
+ rb=106
+ irb=0
+ rbm=2.4
+ re=2.52
+ rc=127
+ cje=1.12e-013
+ vje=0.7591
+ mje=0.5406
+ tf=1.213e-011
+ xtf=2.049
+ vtf=1.813
+ itf=0.04293
+ ptf=0
+ cjc=8.208e-015
+ vjc=0.6666
+ mjc=0.4509
+ xcjc=0.0845
+ tr=4e-011
+ cjs=1.16e-013
+ vjs=0.5286
+ mjs=0.4389
+ xtb=1.022
+ eg=1.12
+ xti=1.78
+ kf=3.5e-016
+ af=1
+ fc=0.8273
 
 
.model PNP8 pnp
 
+ is=7.999e-018
+ bf=141.8
+ nf=1
+ vaf=41.58
+ ikf=0.1085
+ ise=2.233e-015
+ ne=1.505
+ br=32.52
+ nr=1.05
+ var=1.093
+ ikr=5e-005
+ isc=6.621e-016
+ nc=1.15
+ rb=62.46
+ irb=0
+ rbm=2.24
+ re=2.537
+ rc=126
+ cje=9.502e-014
+ vje=0.732
+ mje=0.493
+ tf=1.303e-011
+ xtf=35
+ vtf=3.259
+ itf=0.2639
+ ptf=0
+ cjc=1.08e-013
+ vjc=0.7743
+ mjc=0.5
+ xcjc=0.08504
+ tr=1.5e-010
+ cjs=1.29e-013
+ vjs=0.9058
+ mjs=0.4931
+ xtb=1.732
+ eg=1.12
+ xti=2
+ kf=3.5e-016
+ af=1
+ fc=0.85
 
.ENDS VCA824
 
.subckt VCA82X_BIAS_U5_F8 1 2 3 4  
F_U5_F8         3 4 VF_U5_F8 1
VF_U5_F8         1 2 0V
.ends VCA82X_BIAS_U5_F8
 
.subckt VCA82X_BIAS_U5_F1 1 2 3 4  
F_U5_F1         3 4 VF_U5_F1 1.05
VF_U5_F1         1 2 0V
.ends VCA82X_BIAS_U5_F1
 
.subckt VCA82X_BIAS_U5_F6 1 2 3 4  
F_U5_F6         3 4 VF_U5_F6 1
VF_U5_F6         1 2 0V
.ends VCA82X_BIAS_U5_F6
 
.subckt VCA82X_BIAS_U5_F3 1 2 3 4  
F_U5_F3         3 4 VF_U5_F3 1
VF_U5_F3         1 2 0V
.ends VCA82X_BIAS_U5_F3
 
.subckt VCA82X_BIAS_U5_F4 1 2 3 4  
F_U5_F4         3 4 VF_U5_F4 1
VF_U5_F4         1 2 0V
.ends VCA82X_BIAS_U5_F4
 
.subckt VCA82X_BIAS_U5_F2 1 2 3 4  
F_U5_F2         3 4 VF_U5_F2 1
VF_U5_F2         1 2 0V
.ends VCA82X_BIAS_U5_F2
 
.subckt VCA82X_BIAS_U5_F5 1 2 3 4  
F_U5_F5         3 4 VF_U5_F5 1.05
VF_U5_F5         1 2 0V
.ends VCA82X_BIAS_U5_F5
 
.subckt VCA82X_INPUT_BUFFER_U6_F1 1 2 3 4  
F_U6_F1         3 4 VF_U6_F1 20
VF_U6_F1         1 2 0V
.ends VCA82X_INPUT_BUFFER_U6_F1
 
.subckt VCA821_4_OUTPUT_STAGE_U8_F1 1 2 3 4  
F_U8_F1         3 4 VF_U8_F1 600
VF_U8_F1         1 2 0V
.ends VCA821_4_OUTPUT_STAGE_U8_F1
* TL072 OPERATIONAL AMPLIFIER "MACROMODEL" SUBCIRCUIT
* CREATED USING PARTS RELEASE 4.01 ON 06/16/89 AT 13:08
* (REV N/A)      SUPPLY VOLTAGE: +/-15V
* CONNECTIONS:   NON-INVERTING INPUT
*                | INVERTING INPUT
*                | | POSITIVE POWER SUPPLY
*                | | | NEGATIVE POWER SUPPLY
*                | | | | OUTPUT
*                | | | | |
.SUBCKT TL072    1 2 3 4 5
*
  C1   11 12 3.498E-12
  C2    6  7 15.00E-12
  DC    5 53 DX
  DE   54  5 DX
  DLP  90 91 DX
  DLN  92 90 DX
  DP    4  3 DX
  EGND 99  0 POLY(2) (3,0) (4,0) 0 .5 .5
  FB    7 99 POLY(5) VB VC VE VLP VLN 0 4.715E6 -5E6 5E6 5E6 -5E6
  GA    6  0 11 12 282.8E-6
  GCM   0  6 10 99 8.942E-9
  ISS   3 10 DC 195.0E-6
  HLIM 90  0 VLIM 1K
  J1   11  2 10 JX
  J2   12  1 10 JX
  R2    6  9 100.0E3
  RD1   4 11 3.536E3
  RD2   4 12 3.536E3
  RO1   8  5 150
  RO2   7 99 150
  RP    3  4 2.143E3
  RSS  10 99 1.026E6
  VB    9  0 DC 0
  VC    3 53 DC 2.200
  VE   54  4 DC 2.200
  VLIM  7  8 DC 0
  VLP  91  0 DC 25
  VLN   0 92 DC 25
.MODEL DX D(IS=800.0E-18)
.MODEL JX PJF(IS=15.00E-12 BETA=270.1E-6 VTO=-1)
.ENDS
