ShaunG-RU/DRC-Project/LTspice/RMS Based Compressor/RMS Based Compressor.asc

A1: modulate; mark=1k,space=0.1k
B1: bv; V=(white(2e6*time)/100)
B2: bv; V=(white(2e6*time)/100)
C1: cap; 22p
C2: cap; 100p
C3: cap; 100n
C4: cap; 22p
C5: cap; 10µ
C6: cap; 10µ
C7: cap; 10µ
C8: cap; 22µ
D1: diode; 1N4148
D2: diode; 1N4148
D3: diode; 1N4148
D4: diode; 1N4148
R1: res; 20k
R2: res; 10k
R3: res; 20k; tol=1
R4: res; 10k
R5: res; 10k
R6: res; 10k
R7: res; 1Meg
R8: res; 2k
R9: res; 2k
R10: res; 162k
R13: res; 33k
R14: res; 20k
R15: res; 6.2k
R16: res; 25k
R17: res; 25k
R18: res; 10k
R19: res; 5.1k
R20: res; 1.43k
R21: res; 0
R22: res; 620k
R23: res; 0
R24: res; 10k
R25: res; 10k
THAT1: 4305RMS
THAT2: 4305VCA
U1: OP1177
U2: OP1177
U3: OP1177
U4: OP1177
U5: OP1177
V1: voltage; 15
V2: voltage; -15
V3: voltage; PULSE(0 1 10m 1p 1p 10m 20m)
V4: voltage; 1
V5: voltage; wavefile=test_audio_signal.wav
V6: voltage; PULSE(0 1 20m 1p 1p 20m 40m)
V7: voltage; wavefile=test_audio_signal.wav
V8: voltage; PULSE(0 1 40m 1p 1p 40m 80m)
Named nets: INPUT3, V+, V-, ABS, 0, INPUT, RMS, INPUT2, THRESHOLD, GAIN, VCA, Output
.tran 0.1
.SUBCKT 4305RMS RMS_IN CT RMS_OUT GND V- V+
*
Q_Q6         2 1 RMS_IN QPNPRMS
Q_Q10        3 3 4 QPNPRMS
F_F5         CT V- VF_F5 1
VF_F5        5 V- 0V
F_F3         6 V- VF_F3 1
VF_F3        2 V- 0V
F_F4         V+ 7 VF_F4 1
VF_F4        V+ 6 0V
I_I1         8 V- DC 3.2uA
F_F2         V+ 2 VF_F2 1
VF_F2        V+ 9 0V
Q_Q9         V+ 0 4 QNPNRMS
Q_Q3         9 10 RMS_IN QNPNRMS
E_E1         V+ 10 V+ 11 1
G_G1         11 0 12 13 6.154e-6
R_R1         0 11  22Meg
I_I2         14 5 DC 7.5uA
Q_Q1         13 RMS_IN 8 QNPNRMS 1
R_R4         12 V+  162.5k
R_R3         13 V+  162.5k
C_C1         0 11  4pF
E_E2         10 1 0 3 1
E_E3         15 16 V+ 14 1
E_E5         RMS_OUT 15 CT 15 1
Q_Q2         12 GND 8 QNPNRMS 1
E_E6         15 0 GND 0 1
Q_Q4         7 17 18 QNPNRMS 4
Q_Q7         19 16 18 QPNPRMS 4
Q_Q5         14 14 V+ QPNPRMS 4
R_R6         17 7  700
R_R7         19 16  700
E_E4         20 15 7 15 1
Q_Q8         V+ 20 CT QNPNRMS 4
I_I4         3 V- DC 40nA
I_I5                 V+ V- 370uA
.MODEL QNPNRMS NPN IS=1e-15 BF=200 VAF=800 CJC=.19pF RB=220
.MODEL QPNPRMS PNP IS=1e-15 BF=75 VAF=80 CJC=.53pF RB=205
.ENDS
.SUBCKT 4305VCA VCA_IN VCA_OUT EC- EC+ V+ V- GND
*
R_R11        22 20  30
R_R9         EC+ 34  30
Q_Q35        20 22 24 QNPNVCA
Q_Q42        30 30 31 QNPNVCA
V_V6         1 2 DC 1.4V
D_D5         1 V+ DNOM
Q_Q43        0 0 31 QPNPVCA
Q_Q33        12 9 10 QNHIB
V_V7         2 3 DC .7V
I_I1         10 V- DC 7.0uA
G_G7         28 V- 40 V- 100e-6
E_E1         20 28 30 0 2
Q_Q39        28 28 27 QPNPVCA
Q_Q36        VCA_OUT 34 27 QNPNVCA
R_R36        V- 28  100Meg
Q_Q38        28 28 26 QPNPVCA
I_I9         20 28 DC 130uA
Q_Q41        VCA_OUT EC- 24 QPNPVCA
V_V5         GND 40 DC 1.8V
R_R10        EC- 25  30
V_Vos        9 GND DC 3mV
D_D6         GND 3 DNOM
C_C3         20 0  4.7pF
R_R12        21 20  30
G_G5         V+ 2 11 12 33.65e-6
R_R35        12 V+  15k
R_R34        11 V+  15k
R_R29        GND 2  25Meg
G_G6         V+ 20 2 GND 2.3e-3
C_C4         GND 2 16pF
Q_Q37        20 21 23 QNPNVCA
I_I8         28 V- DC 950uA
I_I10        V+ 6 DC 100uA
D_D7         6 V- DNOM
I_I11        V+ 7 DC 100uA
D_D8         7 V- DNOM
Q_Q40        VCA_IN EC+ 23 QPNPVCA
Q_Q34        VCA_IN 25 26 QNPNVCA
Q_Q32        11 VCA_IN 10 QNHIB
G_G8         VCA_IN V- 6 7 40e-5
I_I2         0 30 DC 22uA
I_Isym       0 34 DC 4.4uA
V_V9                 V+ 4 2.8V
R_R40                4 V- 40k
.model DNOM D Is=1e-14 Cjo=.1pF Rs=.1
.model QNHIB NPN BF=2000
.model QNPNVCA NPN IS=5e-16 BF=150 VAF=150 RB=45 CJC=1.0pF
.model QPNPVCA PNP IS=5e-16 BF=75 VAF=100 RB=100 CJC=1.1pF
.ENDS
Output Buffer
Voltage Controlled Amplifier
Makeup Gain
Threshold Detector
RMS Detector
Precision Full Bridge Rectifier
