ShaunG-RU/DRC-Project/LTspice/Log Converter/Log Converter.asc

A1: modulate; mark=1k space .1k
C1: cap; 300p
C2: cap; 20p
C4: cap; 0.01µ
Q1: npn
Q2: npn
R1: res; 15.7k
R2: res; 2k
R3: res; 1.5Meg
R4: res; 1.5Meg
R5: res; 10k
R6: res; 1k
R7: res; 10k
R8: res; 1Meg
R9: res; 1k
R10: res; 50k
R11: res; 50k
U1: OP1177
U2: OP1177
V1: voltage; 12
V2: voltage; -12
V3: voltage; PULSE(0 1 0 0.5m 0.5m 1p 1p)
V4: voltage; SINE(0 1 1k)
Named nets: 0, V+, V-, Output, Ein
.tran 1
