ShaunG-RU/DRC-Project/STM32/Core/Inc/motor_encoder.h

#ifndef INC_MOTOR_ENCODER_H_
#define INC_MOTOR_ENCODER_H_
#include "stdint.h"
#include "main.h"

typedef struct
{
	int16_t velocity;
	int64_t position;
	uint32_t last_count_value;
}encoder_instance;

void update_encoder(encoder_instance *encoder_value, TIM_HandleTypeDef *htim);
void reset_encoder(encoder_instance *encoder_value);

#endif /* INC_MOTOR_ENCODER_H_ */
